mars3142/PCB_business_card_remake/hardware/LED_Display.kicad_sch

## KiCad design hardware/LED_Display.kicad_sch (2024-11-06)

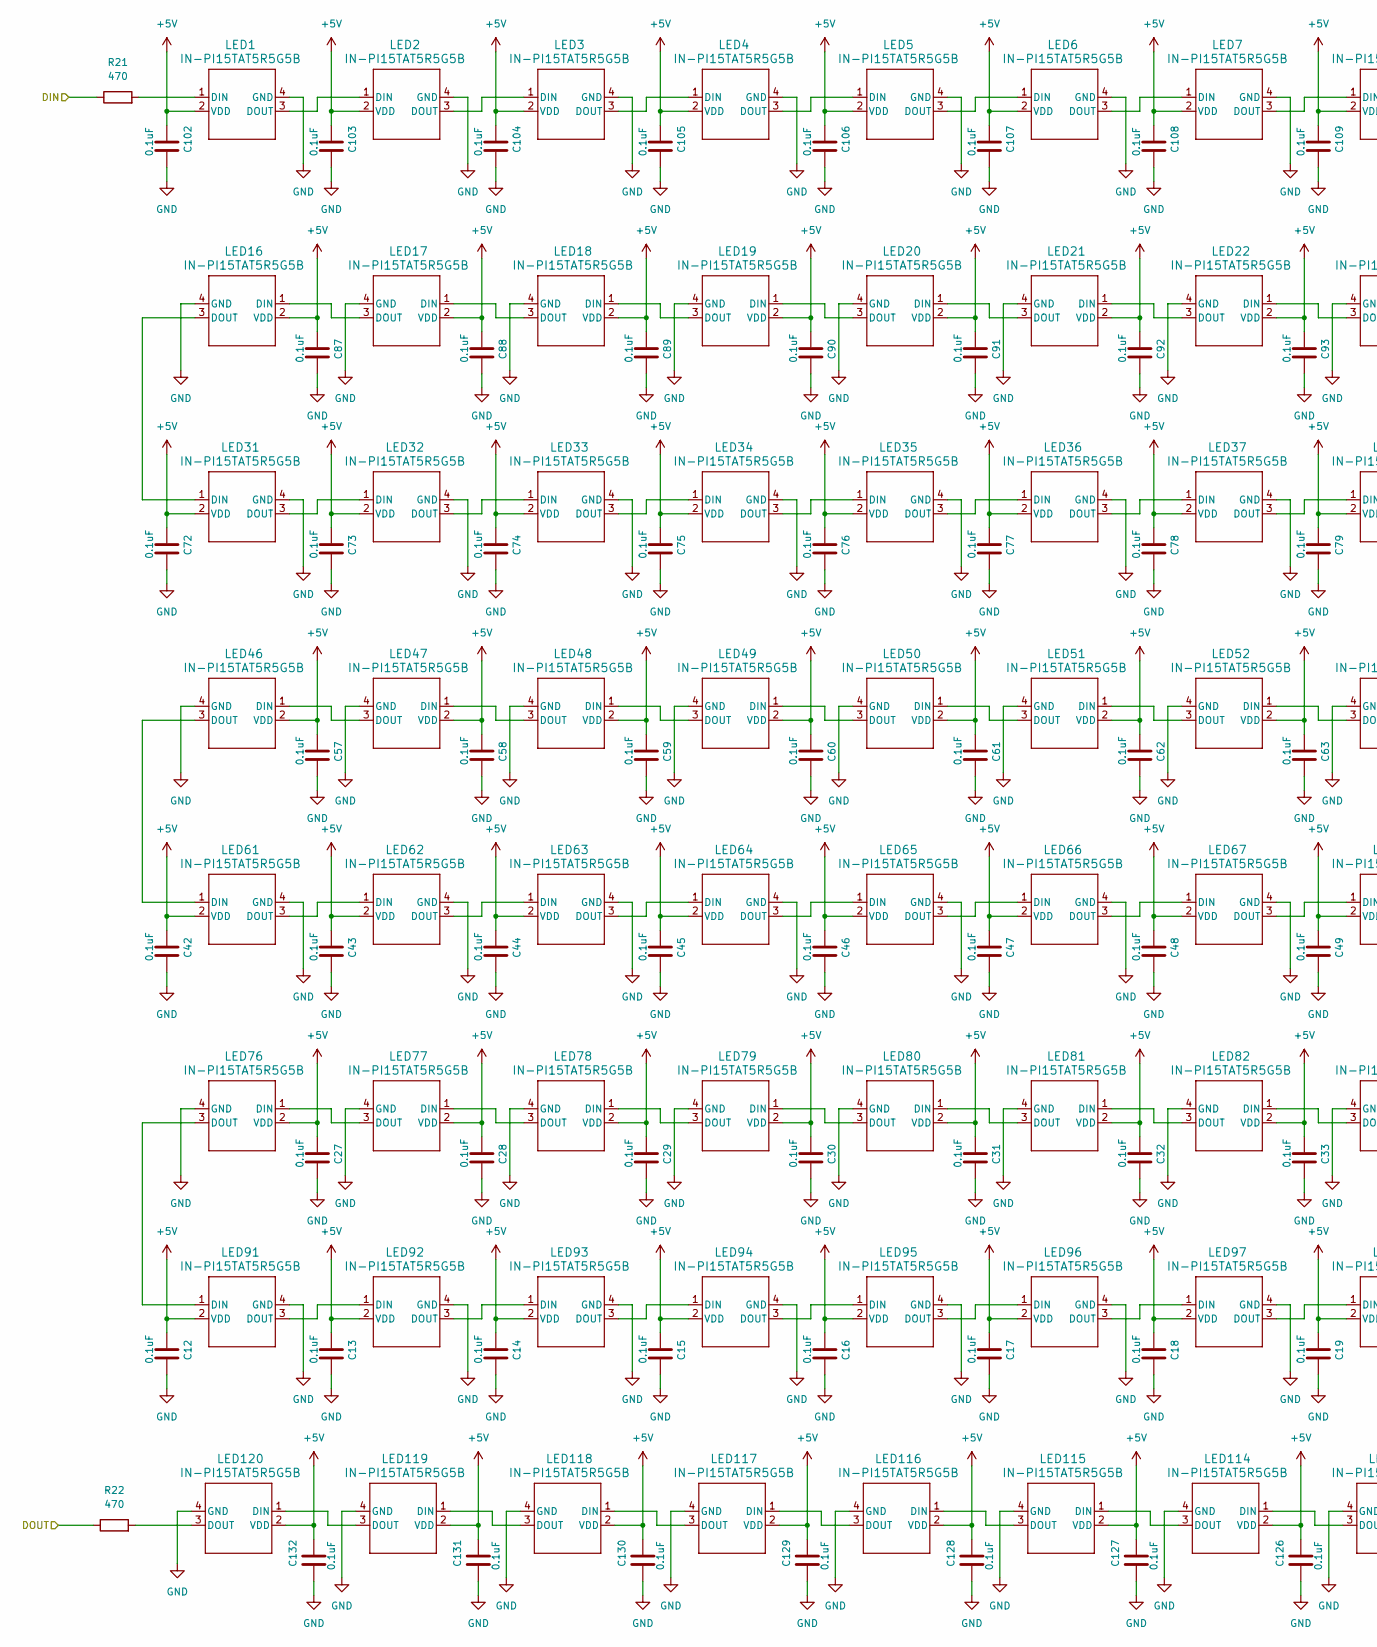
[picture p5: schematic LED_Display.kicad_sch, part in row 1, column 1]

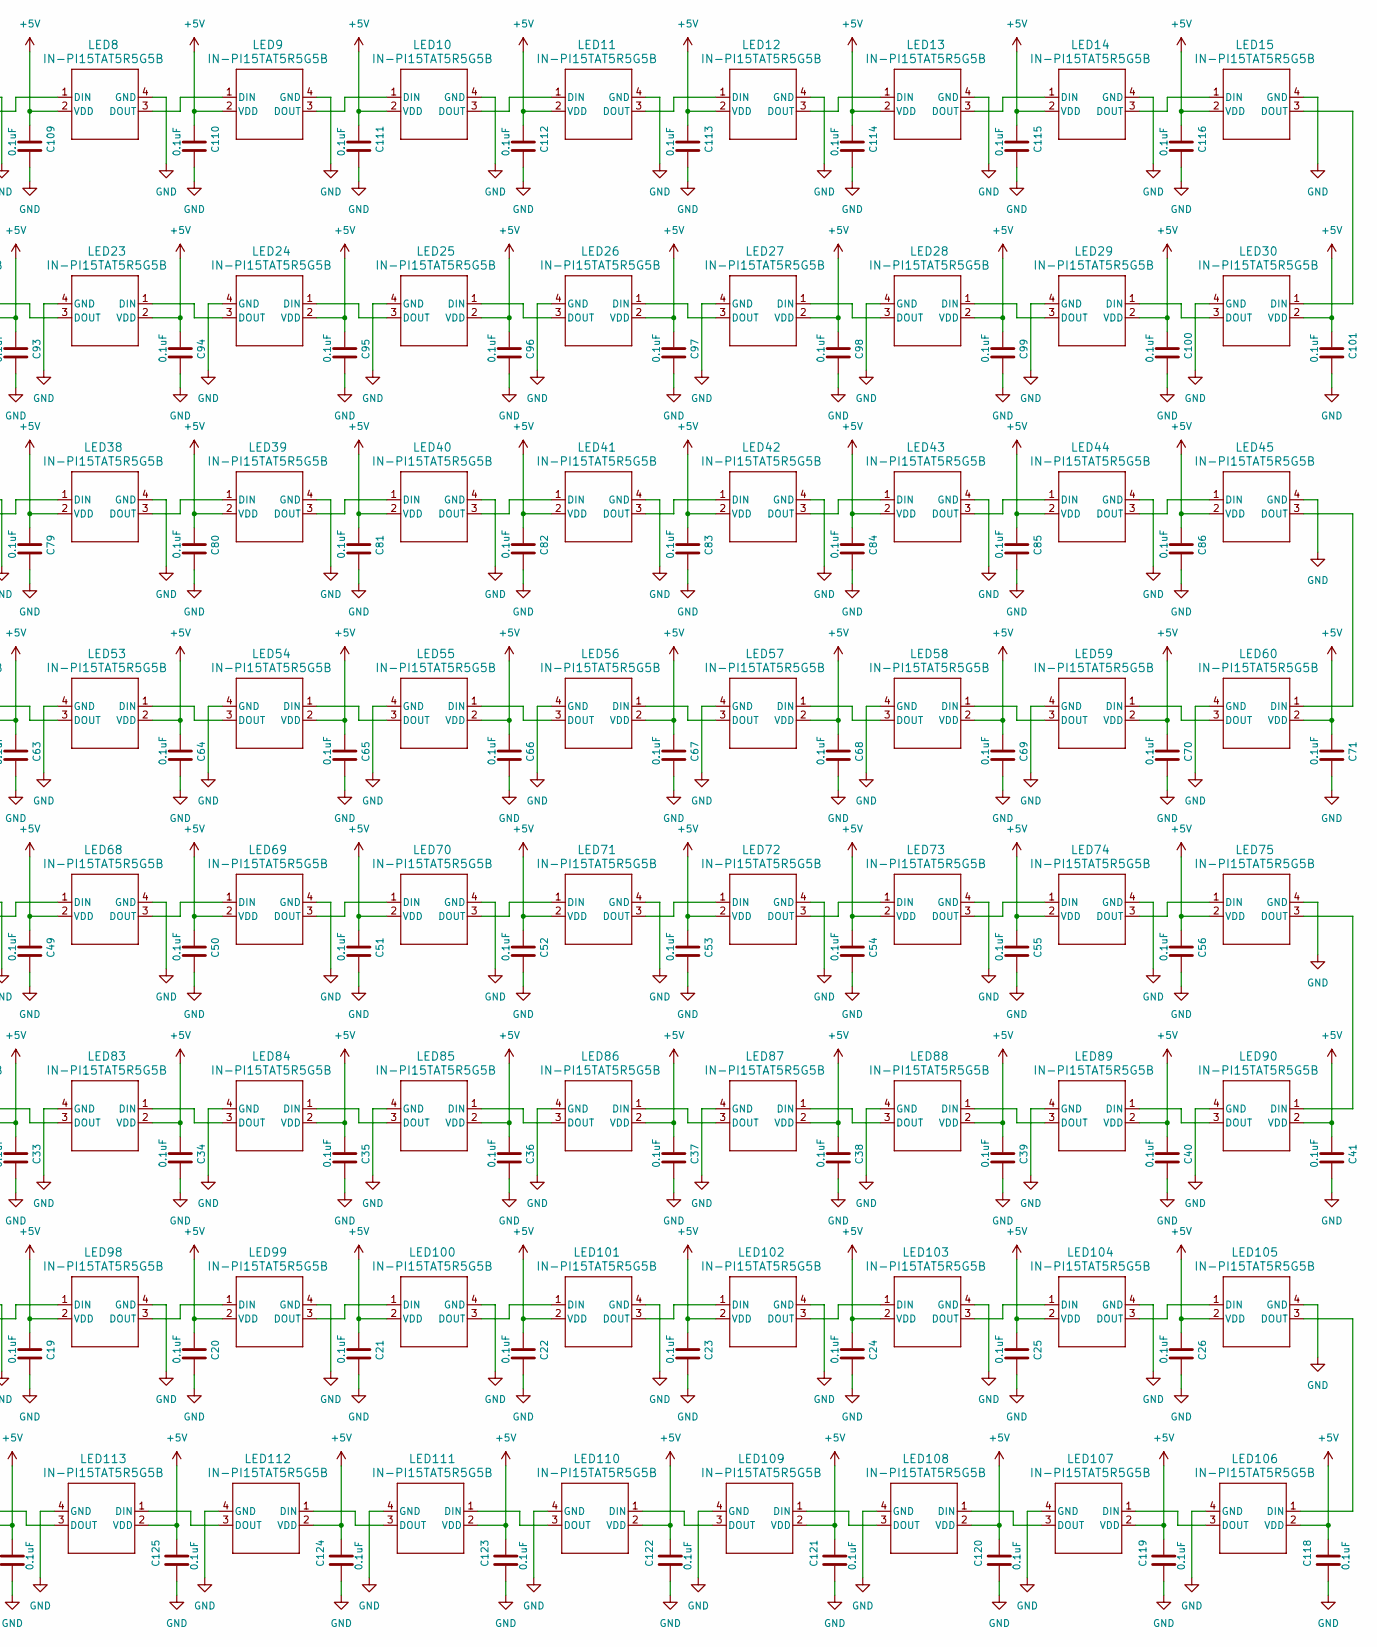
[picture p6: schematic LED_Display.kicad_sch, part in row 1, column 2]

Parts:
C12, C13, C14, C15, C16, C17, C18, C19, C20, C21, C22, C23, C24, C25, C26, C27, C28, C29, C30, C31, C32, C33, C34, C35, C36, C37, C38, C39, C40, C41, C42, C43, C44, C45, C46, C47, C48, C49, C50, C51, C52, C53, C54, C55, C56, C57, C58, C59, C60, C61, C62, C63, C64, C65, C66, C67, C68, C69, C70, C71, C72, C73, C74, C75, C76, C77, C78, C79, C80, C81, C82, C83, C84, C85, C86, C87, C88, C89, C90, C91, C92, C93, C94, C95, C96, C97, C98, C99, C100, C101, C102, C103, C104, C105, C106, C107, C108, C109, C110, C111, C112, C113, C114, C115, C116, C118, C119, C120, C121, C122, C123, C124, C125, C126, C127, C128, C129, C130, C131, C132: 0.1uF; C_0603_1608Metric
LED1, LED2, LED3, LED4, LED5, LED6, LED7, LED8, LED9, LED10, LED11, LED12, LED13, LED14, LED15, LED16, LED17, LED18, LED19, LED20, LED21, LED22, LED23, LED24, LED25, LED26, LED27, LED28, LED29, LED30, LED31, LED32, LED33, LED34, LED35, LED36, LED37, LED38, LED39, LED40, LED41, LED42, LED43, LED44, LED45, LED46, LED47, LED48, LED49, LED50, LED51, LED52, LED53, LED54, LED55, LED56, LED57, LED58, LED59, LED60, LED61, LED62, LED63, LED64, LED65, LED66, LED67, LED68, LED69, LED70, LED71, LED72, LED73, LED74, LED75, LED76, LED77, LED78, LED79, LED80, LED81, LED82, LED83, LED84, LED85, LED86, LED87, LED88, LED89, LED90, LED91, LED92, LED93, LED94, LED95, LED96, LED97, LED98, LED99, LED100, LED101, LED102, LED103, LED104, LED105, LED106, LED107, LED108, LED109, LED110, LED111, LED112, LED113, LED114, LED115, LED116, LED117, LED118, LED119, LED120: IN-PI15TAT5R5G5B; IN-PI15_INL
R21, R22: 470; R_0603_1608Metric

Connections:
+5V: C12.1, C13.1, C14.1, C15.1, C16.1, C17.1, C18.1, C19.1, C20.1, C21.1, C22.1, C23.1, C24.1, C25.1, C26.1, C27.1, C28.1, C29.1, C30.1, C31.1, C32.1, C33.1, C34.1, C35.1, C36.1, C37.1, C38.1, C39.1, C40.1, C41.1, C42.1, C43.1, C44.1, C45.1, C46.1, C47.1, C48.1, C49.1, C50.1, C51.1, C52.1, C53.1, C54.1, C55.1, C56.1, C57.1, C58.1, C59.1, C60.1, C61.1, C62.1, C63.1, C64.1, C65.1, C66.1, C67.1, C68.1, C69.1, C70.1, C71.1, C72.1, C73.1, C74.1, C75.1, C76.1, C77.1, C78.1, C79.1, C80.1, C81.1, C82.1, C83.1, C84.1, C85.1, C86.1, C87.1, C88.1, C89.1, C90.1, C91.1, C92.1, C93.1, C94.1, C95.1, C96.1, C97.1, C98.1, C99.1, C100.1, C101.1, C102.1, C103.1, C104.1, C105.1, C106.1, C107.1, C108.1, C109.1, C110.1, C111.1, C112.1, C113.1, C114.1, C115.1, C116.1, C118.1, C119.1, C120.1, C121.1, C122.1, C123.1, C124.1, C125.1, C126.1, C127.1, C128.1, C129.1, C130.1, C131.1, C132.1, LED1.2 (VDD), LED2.2 (VDD), LED3.2 (VDD), LED4.2 (VDD), LED5.2 (VDD), LED6.2 (VDD), LED7.2 (VDD), LED8.2 (VDD), LED9.2 (VDD), LED10.2 (VDD), LED11.2 (VDD), LED12.2 (VDD), LED13.2 (VDD), LED14.2 (VDD), LED15.2 (VDD), LED16.2 (VDD), LED17.2 (VDD), LED18.2 (VDD), LED19.2 (VDD), LED20.2 (VDD), LED21.2 (VDD), LED22.2 (VDD), LED23.2 (VDD), LED24.2 (VDD), LED25.2 (VDD), LED26.2 (VDD), LED27.2 (VDD), LED28.2 (VDD), LED29.2 (VDD), LED30.2 (VDD), LED31.2 (VDD), LED32.2 (VDD), LED33.2 (VDD), LED34.2 (VDD), LED35.2 (VDD), LED36.2 (VDD), LED37.2 (VDD), LED38.2 (VDD), LED39.2 (VDD), LED40.2 (VDD), LED41.2 (VDD), LED42.2 (VDD), LED43.2 (VDD), LED44.2 (VDD), LED45.2 (VDD), LED46.2 (VDD), LED47.2 (VDD), LED48.2 (VDD), LED49.2 (VDD), LED50.2 (VDD), LED51.2 (VDD), LED52.2 (VDD), LED53.2 (VDD), LED54.2 (VDD), LED55.2 (VDD), LED56.2 (VDD), LED57.2 (VDD), LED58.2 (VDD), LED59.2 (VDD), LED60.2 (VDD), LED61.2 (VDD), LED62.2 (VDD), LED63.2 (VDD), LED64.2 (VDD), LED65.2 (VDD), LED66.2 (VDD), LED67.2 (VDD), LED68.2 (VDD), LED69.2 (VDD), LED70.2 (VDD), LED71.2 (VDD), LED72.2 (VDD), LED73.2 (VDD), LED74.2 (VDD), LED75.2 (VDD), LED76.2 (VDD), LED77.2 (VDD), LED78.2 (VDD), LED79.2 (VDD), LED80.2 (VDD), LED81.2 (VDD), LED82.2 (VDD), LED83.2 (VDD), LED84.2 (VDD), LED85.2 (VDD), LED86.2 (VDD), LED87.2 (VDD), LED88.2 (VDD), LED89.2 (VDD), LED90.2 (VDD), LED91.2 (VDD), LED92.2 (VDD), LED93.2 (VDD), LED94.2 (VDD), LED95.2 (VDD), LED96.2 (VDD), LED97.2 (VDD), LED98.2 (VDD), LED99.2 (VDD), LED100.2 (VDD), LED101.2 (VDD), LED102.2 (VDD), LED103.2 (VDD), LED104.2 (VDD), LED105.2 (VDD), LED106.2 (VDD), LED107.2 (VDD), LED108.2 (VDD), LED109.2 (VDD), LED110.2 (VDD), LED111.2 (VDD), LED112.2 (VDD), LED113.2 (VDD), LED114.2 (VDD), LED115.2 (VDD), LED116.2 (VDD), LED117.2 (VDD), LED118.2 (VDD), LED119.2 (VDD), LED120.2 (VDD)
DIN: R21.1
DOUT: R22.1
GND: C12.2, C13.2, C14.2, C15.2, C16.2, C17.2, C18.2, C19.2, C20.2, C21.2, C22.2, C23.2, C24.2, C25.2, C26.2, C27.2, C28.2, C29.2, C30.2, C31.2, C32.2, C33.2, C34.2, C35.2, C36.2, C37.2, C38.2, C39.2, C40.2, C41.2, C42.2, C43.2, C44.2, C45.2, C46.2, C47.2, C48.2, C49.2, C50.2, C51.2, C52.2, C53.2, C54.2, C55.2, C56.2, C57.2, C58.2, C59.2, C60.2, C61.2, C62.2, C63.2, C64.2, C65.2, C66.2, C67.2, C68.2, C69.2, C70.2, C71.2, C72.2, C73.2, C74.2, C75.2, C76.2, C77.2, C78.2, C79.2, C80.2, C81.2, C82.2, C83.2, C84.2, C85.2, C86.2, C87.2, C88.2, C89.2, C90.2, C91.2, C92.2, C93.2, C94.2, C95.2, C96.2, C97.2, C98.2, C99.2, C100.2, C101.2, C102.2, C103.2, C104.2, C105.2, C106.2, C107.2, C108.2, C109.2, C110.2, C111.2, C112.2, C113.2, C114.2, C115.2, C116.2, C118.2, C119.2, C120.2, C121.2, C122.2, C123.2, C124.2, C125.2, C126.2, C127.2, C128.2, C129.2, C130.2, C131.2, C132.2, LED1.4 (GND), LED2.4 (GND), LED3.4 (GND), LED4.4 (GND), LED5.4 (GND), LED6.4 (GND), LED7.4 (GND), LED8.4 (GND), LED9.4 (GND), LED10.4 (GND), LED11.4 (GND), LED12.4 (GND), LED13.4 (GND), LED14.4 (GND), LED15.4 (GND), LED16.4 (GND), LED17.4 (GND), LED18.4 (GND), LED19.4 (GND), LED20.4 (GND), LED21.4 (GND), LED22.4 (GND), LED23.4 (GND), LED24.4 (GND), LED25.4 (GND), LED26.4 (GND), LED27.4 (GND), LED28.4 (GND), LED29.4 (GND), LED30.4 (GND), LED31.4 (GND), LED32.4 (GND), LED33.4 (GND), LED34.4 (GND), LED35.4 (GND), LED36.4 (GND), LED37.4 (GND), LED38.4 (GND), LED39.4 (GND), LED40.4 (GND), LED41.4 (GND), LED42.4 (GND), LED43.4 (GND), LED44.4 (GND), LED45.4 (GND), LED46.4 (GND), LED47.4 (GND), LED48.4 (GND), LED49.4 (GND), LED50.4 (GND), LED51.4 (GND), LED52.4 (GND), LED53.4 (GND), LED54.4 (GND), LED55.4 (GND), LED56.4 (GND), LED57.4 (GND), LED58.4 (GND), LED59.4 (GND), LED60.4 (GND), LED61.4 (GND), LED62.4 (GND), LED63.4 (GND), LED64.4 (GND), LED65.4 (GND), LED66.4 (GND), LED67.4 (GND), LED68.4 (GND), LED69.4 (GND), LED70.4 (GND), LED71.4 (GND), LED72.4 (GND), LED73.4 (GND), LED74.4 (GND), LED75.4 (GND), LED76.4 (GND), LED77.4 (GND), LED78.4 (GND), LED79.4 (GND), LED80.4 (GND), LED81.4 (GND), LED82.4 (GND), LED83.4 (GND), LED84.4 (GND), LED85.4 (GND), LED86.4 (GND), LED87.4 (GND), LED88.4 (GND), LED89.4 (GND), LED90.4 (GND), LED91.4 (GND), LED92.4 (GND), LED93.4 (GND), LED94.4 (GND), LED95.4 (GND), LED96.4 (GND), LED97.4 (GND), LED98.4 (GND), LED99.4 (GND), LED100.4 (GND), LED101.4 (GND), LED102.4 (GND), LED103.4 (GND), LED104.4 (GND), LED105.4 (GND), LED106.4 (GND), LED107.4 (GND), LED108.4 (GND), LED109.4 (GND), LED110.4 (GND), LED111.4 (GND), LED112.4 (GND), LED113.4 (GND), LED114.4 (GND), LED115.4 (GND), LED116.4 (GND), LED117.4 (GND), LED118.4 (GND), LED119.4 (GND), LED120.4 (GND)
unnamed: LED1.1 (DIN), R21.2
unnamed: LED1.3 (DOUT), LED2.1 (DIN)
unnamed: LED2.3 (DOUT), LED3.1 (DIN)
unnamed: LED3.3 (DOUT), LED4.1 (DIN)
unnamed: LED4.3 (DOUT), LED5.1 (DIN)
unnamed: LED5.3 (DOUT), LED6.1 (DIN)
unnamed: LED6.3 (DOUT), LED7.1 (DIN)
unnamed: LED7.3 (DOUT), LED8.1 (DIN)
unnamed: LED8.3 (DOUT), LED9.1 (DIN)
unnamed: LED9.3 (DOUT), LED10.1 (DIN)
unnamed: LED10.3 (DOUT), LED11.1 (DIN)
unnamed: LED11.3 (DOUT), LED12.1 (DIN)
unnamed: LED12.3 (DOUT), LED13.1 (DIN)
unnamed: LED13.3 (DOUT), LED14.1 (DIN)
unnamed: LED14.3 (DOUT), LED15.1 (DIN)
unnamed: LED15.3 (DOUT), LED30.1 (DIN)
unnamed: LED16.1 (DIN), LED17.3 (DOUT)
unnamed: LED16.3 (DOUT), LED31.1 (DIN)
unnamed: LED17.1 (DIN), LED18.3 (DOUT)
unnamed: LED18.1 (DIN), LED19.3 (DOUT)
unnamed: LED19.1 (DIN), LED20.3 (DOUT)
unnamed: LED20.1 (DIN), LED21.3 (DOUT)
unnamed: LED21.1 (DIN), LED22.3 (DOUT)
unnamed: LED22.1 (DIN), LED23.3 (DOUT)
unnamed: LED23.1 (DIN), LED24.3 (DOUT)
unnamed: LED24.1 (DIN), LED25.3 (DOUT)
unnamed: LED25.1 (DIN), LED26.3 (DOUT)
unnamed: LED26.1 (DIN), LED27.3 (DOUT)
unnamed: LED27.1 (DIN), LED28.3 (DOUT)
unnamed: LED28.1 (DIN), LED29.3 (DOUT)
unnamed: LED29.1 (DIN), LED30.3 (DOUT)
unnamed: LED31.3 (DOUT), LED32.1 (DIN)
unnamed: LED32.3 (DOUT), LED33.1 (DIN)
unnamed: LED33.3 (DOUT), LED34.1 (DIN)
unnamed: LED34.3 (DOUT), LED35.1 (DIN)
unnamed: LED35.3 (DOUT), LED36.1 (DIN)
unnamed: LED36.3 (DOUT), LED37.1 (DIN)
unnamed: LED37.3 (DOUT), LED38.1 (DIN)
unnamed: LED38.3 (DOUT), LED39.1 (DIN)
unnamed: LED39.3 (DOUT), LED40.1 (DIN)
unnamed: LED40.3 (DOUT), LED41.1 (DIN)
unnamed: LED41.3 (DOUT), LED42.1 (DIN)
unnamed: LED42.3 (DOUT), LED43.1 (DIN)
unnamed: LED43.3 (DOUT), LED44.1 (DIN)
unnamed: LED44.3 (DOUT), LED45.1 (DIN)
unnamed: LED45.3 (DOUT), LED60.1 (DIN)
unnamed: LED46.1 (DIN), LED47.3 (DOUT)
unnamed: LED46.3 (DOUT), LED61.1 (DIN)
unnamed: LED47.1 (DIN), LED48.3 (DOUT)
unnamed: LED48.1 (DIN), LED49.3 (DOUT)
unnamed: LED49.1 (DIN), LED50.3 (DOUT)
unnamed: LED50.1 (DIN), LED51.3 (DOUT)
unnamed: LED51.1 (DIN), LED52.3 (DOUT)
unnamed: LED52.1 (DIN), LED53.3 (DOUT)
unnamed: LED53.1 (DIN), LED54.3 (DOUT)
unnamed: LED54.1 (DIN), LED55.3 (DOUT)
unnamed: LED55.1 (DIN), LED56.3 (DOUT)
unnamed: LED56.1 (DIN), LED57.3 (DOUT)
unnamed: LED57.1 (DIN), LED58.3 (DOUT)
unnamed: LED58.1 (DIN), LED59.3 (DOUT)
unnamed: LED59.1 (DIN), LED60.3 (DOUT)
unnamed: LED61.3 (DOUT), LED62.1 (DIN)
unnamed: LED62.3 (DOUT), LED63.1 (DIN)
unnamed: LED63.3 (DOUT), LED64.1 (DIN)
unnamed: LED64.3 (DOUT), LED65.1 (DIN)
unnamed: LED65.3 (DOUT), LED66.1 (DIN)
unnamed: LED66.3 (DOUT), LED67.1 (DIN)
unnamed: LED67.3 (DOUT), LED68.1 (DIN)
unnamed: LED68.3 (DOUT), LED69.1 (DIN)
unnamed: LED69.3 (DOUT), LED70.1 (DIN)
unnamed: LED70.3 (DOUT), LED71.1 (DIN)
unnamed: LED71.3 (DOUT), LED72.1 (DIN)
unnamed: LED72.3 (DOUT), LED73.1 (DIN)
unnamed: LED73.3 (DOUT), LED74.1 (DIN)
unnamed: LED74.3 (DOUT), LED75.1 (DIN)
unnamed: LED75.3 (DOUT), LED90.1 (DIN)
unnamed: LED76.1 (DIN), LED77.3 (DOUT)
unnamed: LED76.3 (DOUT), LED91.1 (DIN)
unnamed: LED77.1 (DIN), LED78.3 (DOUT)
unnamed: LED78.1 (DIN), LED79.3 (DOUT)
unnamed: LED79.1 (DIN), LED80.3 (DOUT)
unnamed: LED80.1 (DIN), LED81.3 (DOUT)
unnamed: LED81.1 (DIN), LED82.3 (DOUT)
unnamed: LED82.1 (DIN), LED83.3 (DOUT)
unnamed: LED83.1 (DIN), LED84.3 (DOUT)
unnamed: LED84.1 (DIN), LED85.3 (DOUT)
unnamed: LED85.1 (DIN), LED86.3 (DOUT)
unnamed: LED86.1 (DIN), LED87.3 (DOUT)
unnamed: LED87.1 (DIN), LED88.3 (DOUT)
unnamed: LED88.1 (DIN), LED89.3 (DOUT)
unnamed: LED89.1 (DIN), LED90.3 (DOUT)
unnamed: LED91.3 (DOUT), LED92.1 (DIN)
unnamed: LED92.3 (DOUT), LED93.1 (DIN)
unnamed: LED93.3 (DOUT), LED94.1 (DIN)
unnamed: LED94.3 (DOUT), LED95.1 (DIN)
unnamed: LED95.3 (DOUT), LED96.1 (DIN)
unnamed: LED96.3 (DOUT), LED97.1 (DIN)
unnamed: LED97.3 (DOUT), LED98.1 (DIN)
unnamed: LED98.3 (DOUT), LED99.1 (DIN)
unnamed: LED99.3 (DOUT), LED100.1 (DIN)
unnamed: LED100.3 (DOUT), LED101.1 (DIN)
unnamed: LED101.3 (DOUT), LED102.1 (DIN)
unnamed: LED102.3 (DOUT), LED103.1 (DIN)
unnamed: LED103.3 (DOUT), LED104.1 (DIN)
unnamed: LED104.3 (DOUT), LED105.1 (DIN)
unnamed: LED105.3 (DOUT), LED106.1 (DIN)
unnamed: LED106.3 (DOUT), LED107.1 (DIN)
unnamed: LED107.3 (DOUT), LED108.1 (DIN)
unnamed: LED108.3 (DOUT), LED109.1 (DIN)
unnamed: LED109.3 (DOUT), LED110.1 (DIN)
unnamed: LED110.3 (DOUT), LED111.1 (DIN)
unnamed: LED111.3 (DOUT), LED112.1 (DIN)
unnamed: LED112.3 (DOUT), LED113.1 (DIN)
unnamed: LED113.3 (DOUT), LED114.1 (DIN)
unnamed: LED114.3 (DOUT), LED115.1 (DIN)
unnamed: LED115.3 (DOUT), LED116.1 (DIN)
unnamed: LED116.3 (DOUT), LED117.1 (DIN)
unnamed: LED117.3 (DOUT), LED118.1 (DIN)
unnamed: LED118.3 (DOUT), LED119.1 (DIN)
unnamed: LED119.3 (DOUT), LED120.1 (DIN)
unnamed: LED120.3 (DOUT), R22.2
