mars3142/PCB_business_card_remake/hardware/PCB_business_card.kicad_sch

## KiCad design hardware/PCB_business_card.kicad_sch (2024-11-06)

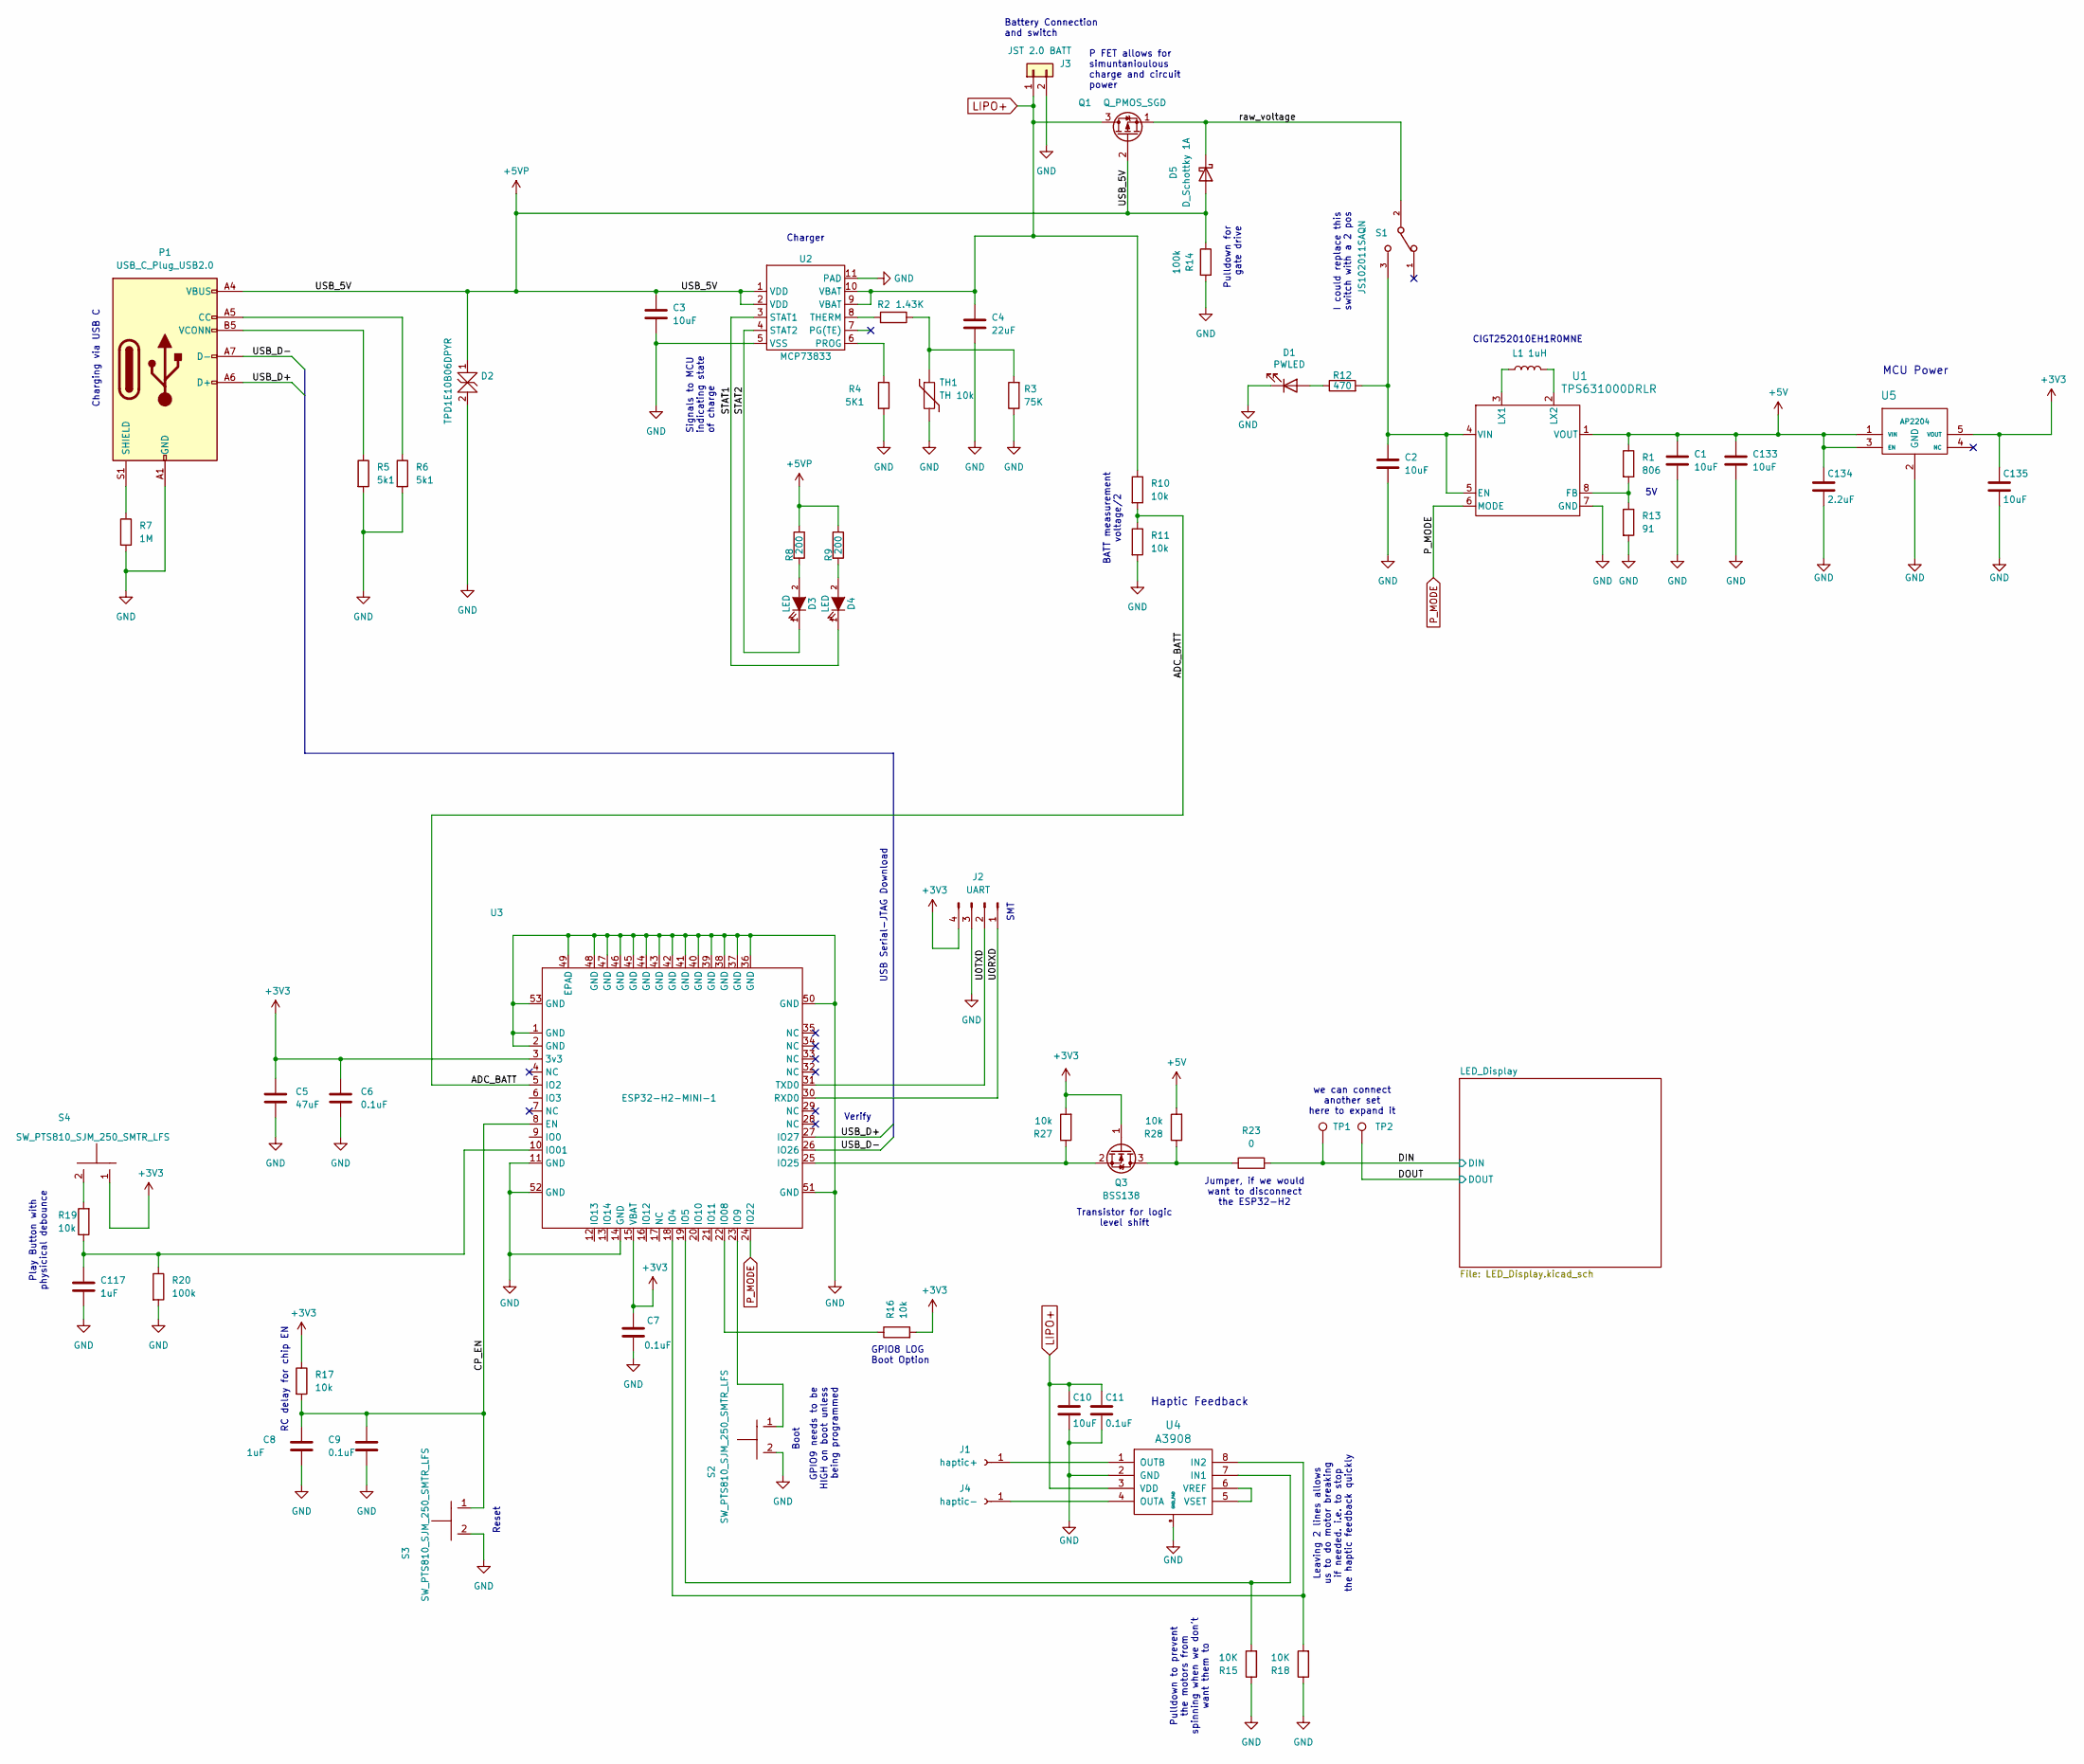
[picture p7: schematic PCB_business_card.kicad_sch]

Parts:
C1, C2, C3, C10, C133, C135: 10uF; C_0603_1608Metric
C4: 22uF; C_0603_1608Metric
C5: 47uF; C_0603_1608Metric
C6, C7, C9, C11: 0.1uF; C_0603_1608Metric
C8, C117: 1uF; C_0603_1608Metric
C134: 2.2uF; C_0603_1608Metric
D1: PWLED; D_0603_1608Metric
D2: TPD1E10B06DPYR; D_SOD-523
D3, D4: LED; D_0603_1608Metric
D5: D_Schottky 1A; D_SMA
J1: haptic+; TestPoint_Pad_2.0x2.0mm
J2: UART; PinHeader_1x04_P2.54mm_Vertical_SMD_Pin1Left
J3: JST 2.0 BATT; JST_PH_S2B-PH-SM4-TB_1x02-1MP_P2.00mm_Horizontal
J4: haptic-; TestPoint_Pad_2.0x2.0mm
L1: 1uH; RES_CIGT252010
P1: USB_C_Plug_USB2.0; GCT_USB4105-GF-A
Q1: Q_PMOS_SGD; SOT-23-DMG2301
Q3: BSS138; SOT-23
R1: 806; R_0603_1608Metric
R2: 1.43K; R_0603_1608Metric
R3: 75K; R_0603_1608Metric
R4: 5K1; R_0603_1608Metric
R5, R6: 5k1; R_0603_1608Metric
R7: 1M; R_0603_1608Metric
R8, R9: 200; R_0603_1608Metric
R10, R11, R16, R17, R19, R27, R28: 10k; R_0603_1608Metric
R12: 470; R_0603_1608Metric
R13: 91; R_0603_1608Metric
R14, R20: 100k; R_0603_1608Metric
R15, R18: 10K; R_0603_1608Metric
R23: 0; R_0603_1608Metric
S1: JS102011SAQN; SW_JS102011SAQN
S2, S3, S4: SW_PTS810_SJM_250_SMTR_LFS
TH1: TH 10k; R_0603_1608Metric
TP1, TP2: TestPoint; TestPoint_Pad_2.0x2.0mm
U1: TPS631000DRLR; TPS631000DRLR_TEX
U2: MCP73833; SON50P300X300X100-11N
U3: ESP32-H2-MINI-1; MODULE_ESP32-H2-MINI-1-H2
U4: A3908
U5: AP2204

Connections:
+3V3: C5.1, C6.1, C7.1, C135.1, J2.4, Q3.1 (G), R16.2, R17.1, R27.2, S4.1, U3.3 (3v3), U3.15 (VBAT), U5.5 (VOUT)
+5V: C1.1, C133.1, C134.1, R1.1, R28.2, U1.1 (VOUT), U5.1 (VIN), U5.3 (EN)
+5VP: C3.1, D2.1, D5.2 (A), P1.A4 (VBUS), P1.A9 (VBUS), P1.B4 (VBUS), P1.B9 (VBUS), Q1.2 (G), R8.1, R9.1, R14.1, U2.1 (VDD), U2.2 (VDD)
ADC_BATT: R10.2, R11.1, U3.5 (IO2)
CP_EN: C8.1, C9.1, R17.2, S3.1, U3.8 (EN)
DIN: R23.2, TP1.1
DOUT: TP2.1
GND: C1.2, C2.2, C3.2, C4.2, C5.2, C6.2, C7.2, C8.2, C9.2, C10.2, C11.2, C117.2, C133.2, C134.2, C135.2, D1.1 (K), D2.2, J2.3, J3.2, P1.A1 (GND), P1.A12 (GND), P1.B1 (GND), P1.B12 (GND), R3.1, R4.2, R5.2, R6.2, R7.2, R11.2, R13.2, R14.2, R15.1, R18.1, R20.2, S2.2, S3.2, TH1.2, U1.7 (GND), U2.5 (VSS), U2.11 (PAD), U3.1 (GND), U3.2 (GND), U3.11 (GND), U3.14 (GND), U3.36 (GND), U3.37 (GND), U3.38 (GND), U3.39 (GND), U3.40 (GND), U3.41 (GND), U3.42 (GND), U3.43 (GND), U3.44 (GND), U3.45 (GND), U3.46 (GND), U3.47 (GND), U3.48 (GND), U3.49 (EPAD), U3.50 (GND), U3.51 (GND), U3.52 (GND), U3.53 (GND), U4.2 (GND), U4.9 (GND_PAD), U5.2 (GND)
LIPO+: C4.1, C10.1, C11.1, J3.1, Q1.3 (D), R10.1, U2.9 (VBAT), U2.10 (VBAT), U4.3 (VDD)
unnamed: C2.1, R12.2, S1.3, U1.4 (VIN), U1.5 (EN)
unnamed: C117.1, R19.1, R20.1, U3.10 (IO01)
unnamed: D1.2 (A), R12.1
unnamed: D3.2 (A), R8.2
unnamed: D4.2 (A), R9.2
unnamed: J1.1, U4.1 (OUTB)
unnamed: J4.1, U4.4 (OUTA)
unnamed: L1.1, U1.3 (LX1)
unnamed: L1.2, U1.2 (LX2)
unnamed: P1.A5 (CC), R6.1
unnamed: P1.B5 (VCONN), R5.1
unnamed: P1.S1 (SHIELD), R7.1
unnamed: Q3.2 (S), R27.1, U3.25 (IO25)
unnamed: Q3.3 (D), R23.1, R28.1
unnamed: R1.2, R13.1, U1.8 (FB)
unnamed: R2.1, R3.2, TH1.1
unnamed: R2.2, U2.8 (THERM)
unnamed: R4.1, U2.6 (PROG)
unnamed: R15.2, U3.19 (IO5), U4.7 (IN1)
unnamed: R16.1, U3.22 (IO08)
unnamed: R18.2, U3.18 (IO4), U4.8 (IN2)
unnamed: R19.2, S4.2
unnamed: S2.1, U3.23 (IO9)
unnamed: U4.5 (VSET), U4.6 (VREF)
P_MODE: U1.6 (MODE), U3.24 (IO22)
STAT1: D4.1 (K), U2.3 (STAT1)
STAT2: D3.1 (K), U2.4 (STAT2)
U0RXD: J2.1, U3.30 (RXD0)
U0TXD: J2.2, U3.31 (TXD0)
USB_D+: P1.A6 (D+), U3.27 (IO27)
USB_D-: P1.A7 (D-), U3.26 (IO26)
raw_voltage: D5.1 (K), Q1.1 (S), S1.2

Notes on the sheet:
Jumper, if we would want to disconnect the ESP32-H2
Boot
GPIO8 LOG Boot Option
Signals to MCU indicating state of charge
I could replace this switch with a 2 pos
Reset
RC delay for chip EN
SMT
GPIO9 needs to be HIGH on boot unless being programmed
Verify
MCU Power
Leaving 2 lines allows us to do motor breaking if needed. i.e. to stop the haptic feedback quickly
Haptic Feedback
Pulldown to prevent the motors from spinning when we don't want them to
Pulldown for gate drive
we can connect another set here to expand it
BATT measurement voltage/2
USB Serial-JTAG Download
Charger
Charging via USB C
Transistor for logic level shift
Play Button with physicical debounce
Battery Connection and switch
CIGT252010EH1R0MNE
P FET allows for simuntanioulous charge and circuit power
