mars3142/PCB_business_card_remake/firmware/main/ws2812_control.c

#include "ws2812_control.h"
#include "driver/rmt.h"
#include "esp_err.h"
#include "esp_check.h"

// Configure these based on your project needs using menuconfig ********
#define LED_RMT_TX_CHANNEL		0
#define LED_RMT_TX_GPIO			25
// ****************************************************

#define BITS_PER_LED_CMD	24

#define LED_BUFFER_ITEMS	(NUM_LEDS * BITS_PER_LED_CMD)

// assuming 96mHz

// These values are determined by measuring pulse timing with logic analyzer and adjusting to match datasheet. 
#define T0H	14  // 0 bit high time (0.3 * 96/2)
#define T1H	29 // 1 bit high time (0.6 * 96/2)
#define T0L	38 // low time for either bit (0.8 * 96/2)
#define T1L	10 // (0.2 * 96/2)

// Tag for log messages
static const char *TAG = "NeoPixel WS2812 Driver";

// This is the buffer which the hw peripheral will access while pulsing the output pin
static rmt_item32_t led_data_buffer[LED_BUFFER_ITEMS];

static void setup_rmt_data_buffer(struct led_state new_state);

esp_err_t ws2812_control_init(void)
{
  rmt_config_t config = {
    .rmt_mode = RMT_MODE_TX,
    .channel = LED_RMT_TX_CHANNEL,
    .gpio_num = LED_RMT_TX_GPIO,
    .mem_block_num = 3,
    .tx_config.loop_en = false,
    .tx_config.carrier_en = false,
    .tx_config.idle_output_en = true,
    .tx_config.idle_level = 0,
    .clk_div = 1
  };

  ESP_RETURN_ON_ERROR(rmt_config(&config), TAG, "Failed to configure RMT");
  ESP_RETURN_ON_ERROR(rmt_driver_install(config.channel, 0, 0), TAG, "Failed to install RMT driver");

  return ESP_OK;
}

esp_err_t ws2812_write_leds(struct led_state new_state)
{
  setup_rmt_data_buffer(new_state);
  ESP_RETURN_ON_ERROR(rmt_write_items(LED_RMT_TX_CHANNEL, led_data_buffer, LED_BUFFER_ITEMS, false), TAG, "Failed to write items");
  ESP_RETURN_ON_ERROR(rmt_wait_tx_done(LED_RMT_TX_CHANNEL, portMAX_DELAY), TAG, "Failed to wait for RMT transmission to finish");

  return ESP_OK;
}

static void setup_rmt_data_buffer(struct led_state new_state)
{
  for (uint32_t led = 0; led < NUM_LEDS; led++) {
    uint32_t bits_to_send = new_state.leds[led];
    uint32_t mask = 1 << (BITS_PER_LED_CMD - 1);

//    ESP_LOGI(TAG, "LED %u: bits_to_send = 0x%08X", led, bits_to_send);

    for (uint32_t bit = 0; bit < BITS_PER_LED_CMD; bit++) {
      uint32_t bit_is_set = bits_to_send & mask;
      led_data_buffer[(led * BITS_PER_LED_CMD) + bit] = bit_is_set ?
                                                      (rmt_item32_t){{{T1H, 1, T1L, 0}}} :
                                                      (rmt_item32_t){{{T0H, 1, T0L, 0}}};

//      ESP_LOGI(TAG, "  Bit %u: %s (mask: 0x%08X)", bit, bit_is_set ? "SET" : "UNSET", mask);

      mask >>= 1;
    }
  }
}
