mars3142/PCB_business_card_remake/firmware/main/gap.h

#pragma once

#include "esp_log.h"
#include "host/ble_hs.h"
#include "nimble/ble.h"
#include "nimble/nimble_port.h"
#include "nimble/nimble_port_freertos.h"

#define LOG_TAG_GAP "gap"

static const char device_name[] = "PCBBusinessCard";

void advertise();
void reset_cb(int reason);
void sync_cb(void);
void host_task(void *param);
