mars3142/PCB_business_card_remake/firmware/main/game.h

#ifndef PCB_BUSINESS_CARD_REMAKE_GAME_H
#define PCB_BUSINESS_CARD_REMAKE_GAME_H

#include <stdint.h>

extern uint32_t game_background[8][15];
extern uint32_t game_pipes[8][15];

void game_compile_buffer(uint32_t buffer[8][15]);
uint32_t game_get_game_over(void);
uint32_t game_get_score(void);
void game_reset(void);
void game_run(void);


#endif //PCB_BUSINESS_CARD_REMAKE_GAME_H
